Gustbel/F5k-PcbDesign/Frost5000-Archivos_Fuente_Altium/LibraryUsed/Originales/STEP_Models/Cap1210.step

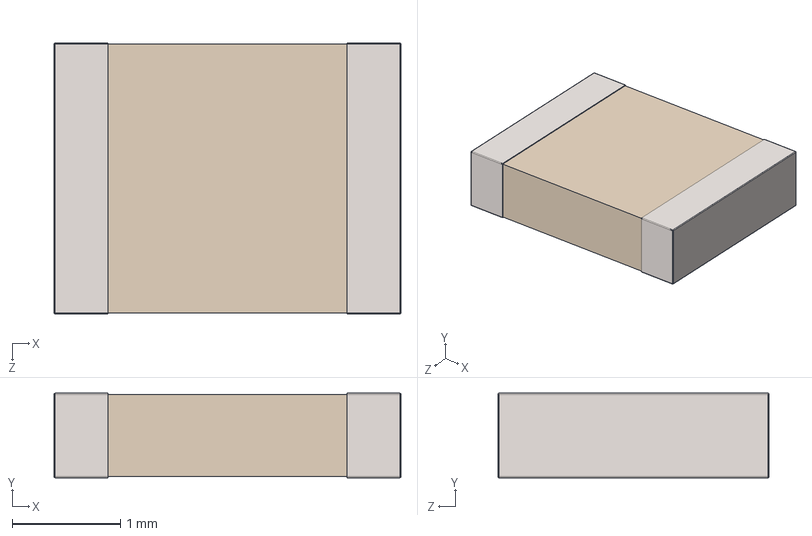
[picture p18: CAD file, 2020-05-13]
Frost5000-Archivos_Fuente_Altium/LibraryUsed/Originales/STEP_Models/Cap1210.step
3.20 x 0.78 x 2.50 mm
