Gustbel/F5k-PcbDesign/Frost5000-Archivos_Fuente_Altium/LibraryUsed/Originales/STEP_Models/W25Q32JV_SOIC-8-208.STEP

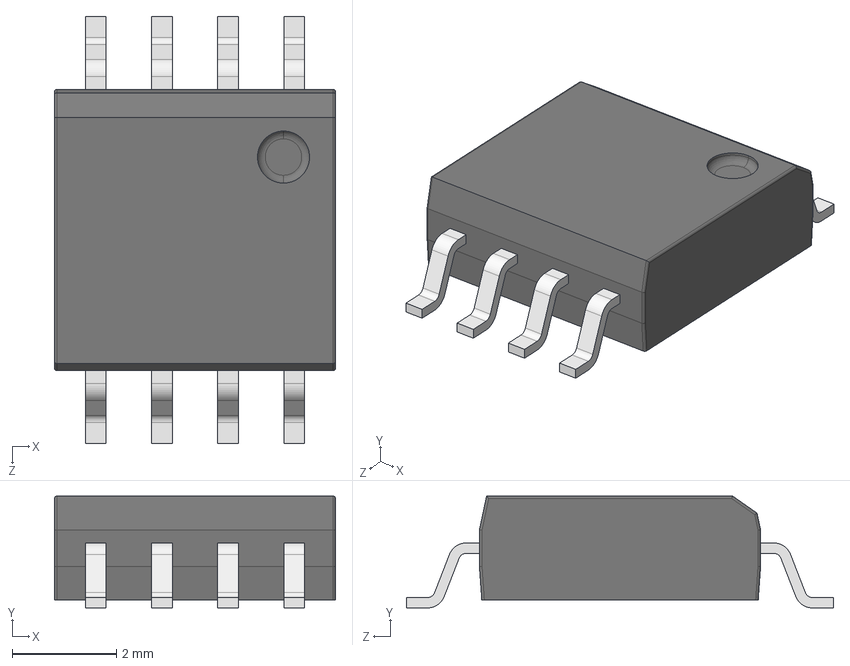
[picture p19: CAD file, 2020-05-13]
Frost5000-Archivos_Fuente_Altium/LibraryUsed/Originales/STEP_Models/W25Q32JV_SOIC-8-208.STEP
5.40 x 2.15 x 8.20 mm
pin_SOIC_SOIC-208_1 x 8
SOIC_150_SOIC_5.4x5.4_1
