Gustbel/F5k-PcbDesign/Frost5000-Archivos_Fuente_Altium/LibraryUsed/Originales/STEP_Models/ABM8-26MHz.STEP

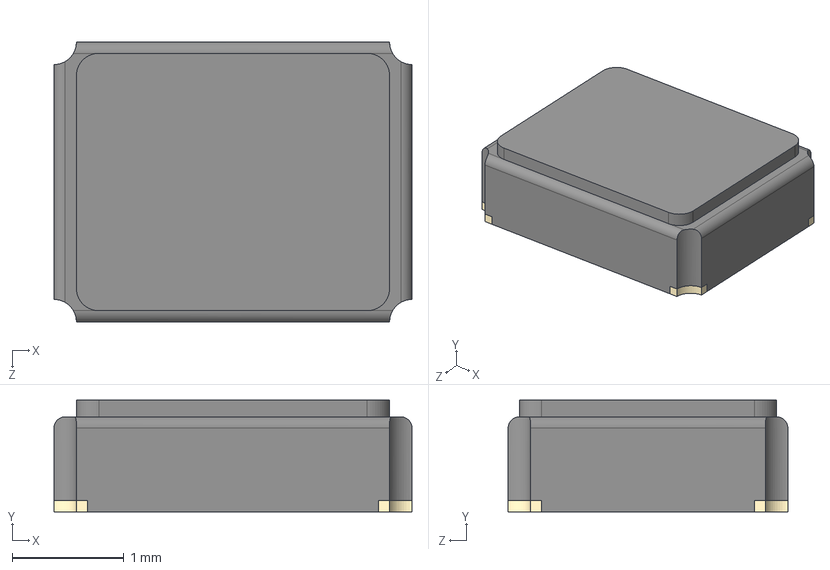
[picture p20: CAD file, 2020-05-13]
Frost5000-Archivos_Fuente_Altium/LibraryUsed/Originales/STEP_Models/ABM8-26MHz.STEP
3.20 x 1.00 x 2.50 mm
