Gustbel/F5k-PcbDesign/Frost5000-Archivos_Fuente_Altium/LibraryUsed/Originales/STEP_Models/Header_127mm_Pitch2-1_usar2.step

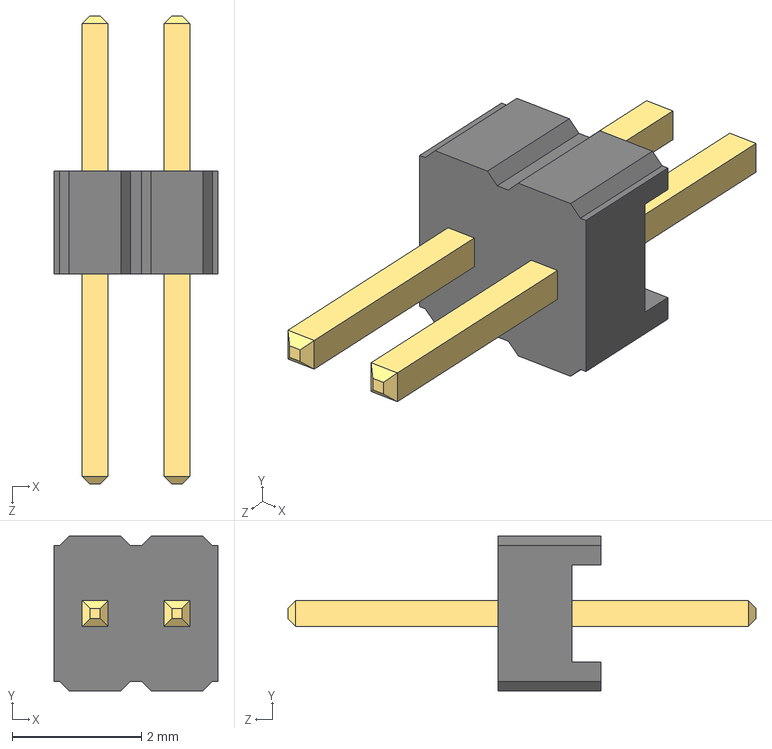
[picture p21: CAD file, 2020-05-13]
Frost5000-Archivos_Fuente_Altium/LibraryUsed/Originales/STEP_Models/Header_127mm_Pitch2-1_usar2.step
2.54 x 2.40 x 7.25 mm
