Gustbel/F5k-PcbDesign/Frost5000-Archivos_Fuente_Altium/LibraryUsed/Originales/STEP_Models/PT2512FK-070R1L.STEP

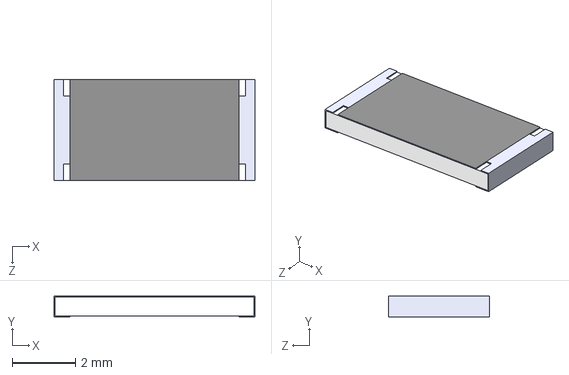
[picture p22: CAD file, 2020-05-13]
Frost5000-Archivos_Fuente_Altium/LibraryUsed/Originales/STEP_Models/PT2512FK-070R1L.STEP
6.35 x 0.65 x 3.20 mm
