Gustbel/F5k-PcbDesign/Frost5000-Archivos_Fuente_Altium/LibraryUsed/Originales/STEP_Models/Header_254mm_Pitch2-1.step

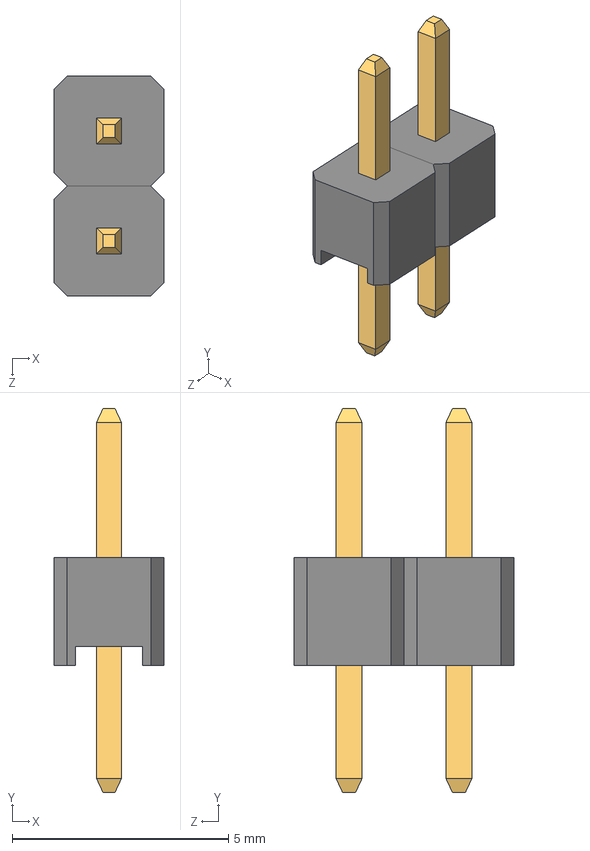
[picture p25: CAD file, 2020-05-13]
Frost5000-Archivos_Fuente_Altium/LibraryUsed/Originales/STEP_Models/Header_254mm_Pitch2-1.step
2.54 x 8.88 x 5.08 mm
