Gustbel/F5k-PcbDesign/Frost5000-Archivos_Fuente_Altium/LibraryUsed/Originales/STEP_Models/ESP8266EX.STEP

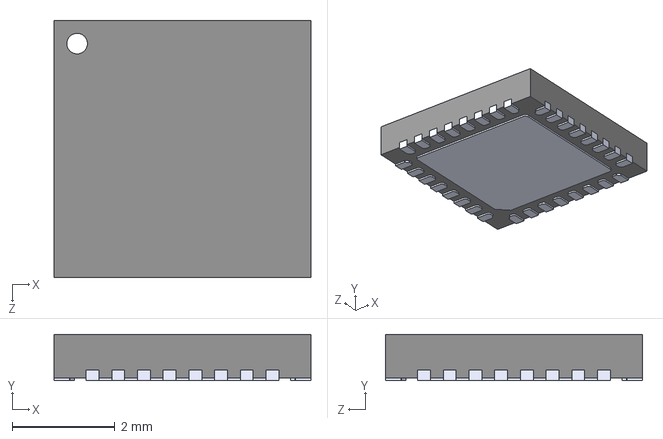
[picture p26: CAD file, 2020-05-13]
Frost5000-Archivos_Fuente_Altium/LibraryUsed/Originales/STEP_Models/ESP8266EX.STEP
5.00 x 0.9 x 5.00 mm
