Gustbel/F5k-PcbDesign/Frost5000-Archivos_Fuente_Altium/LibraryUsed/Originales/STEP_Models/LED_HSMW-C191.STEP

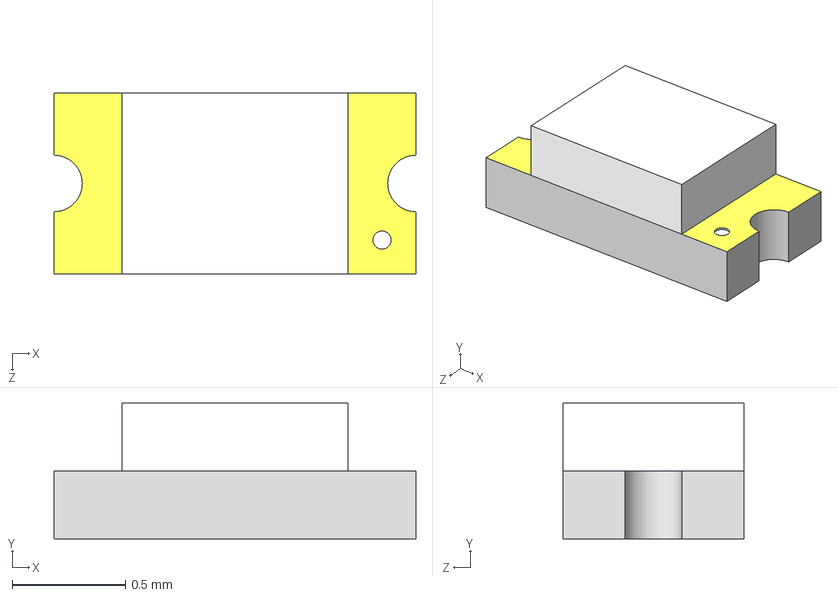
[picture p28: CAD file, 2020-05-13]
Frost5000-Archivos_Fuente_Altium/LibraryUsed/Originales/STEP_Models/LED_HSMW-C191.STEP
1.60 x 0.6 x 0.8 mm
